SRA-VJTI/sra-board-hardware-design/documentation/assets/3d_side_view.png

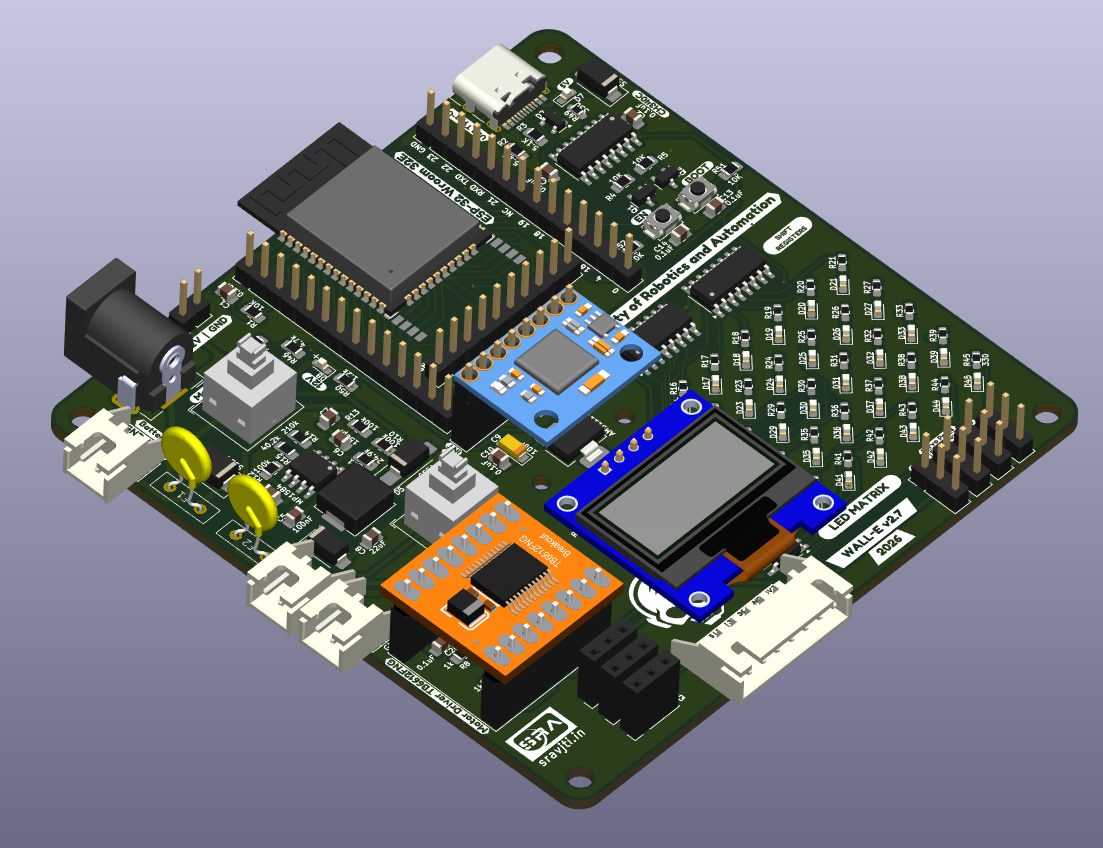
documentation/assets/3d_side_view.png
