SRA-VJTI/sra-board-hardware-design/documentation/assets/A4988_Stepper_Motor.png

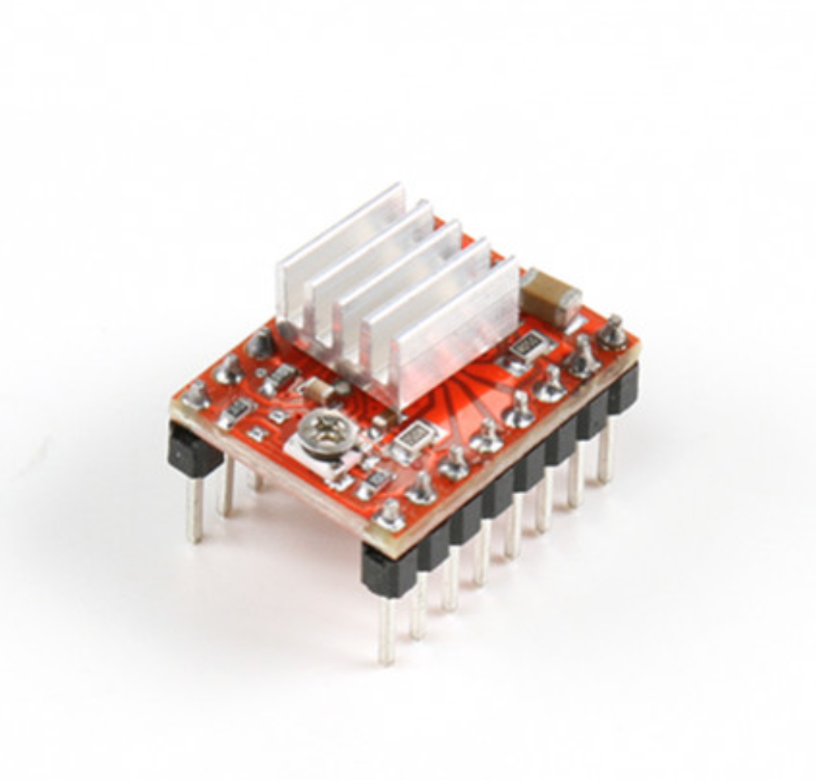
documentation/assets/A4988_Stepper_Motor.png
