SRA-VJTI/sra-board-hardware-design/documentation/assets/diode_vin.png

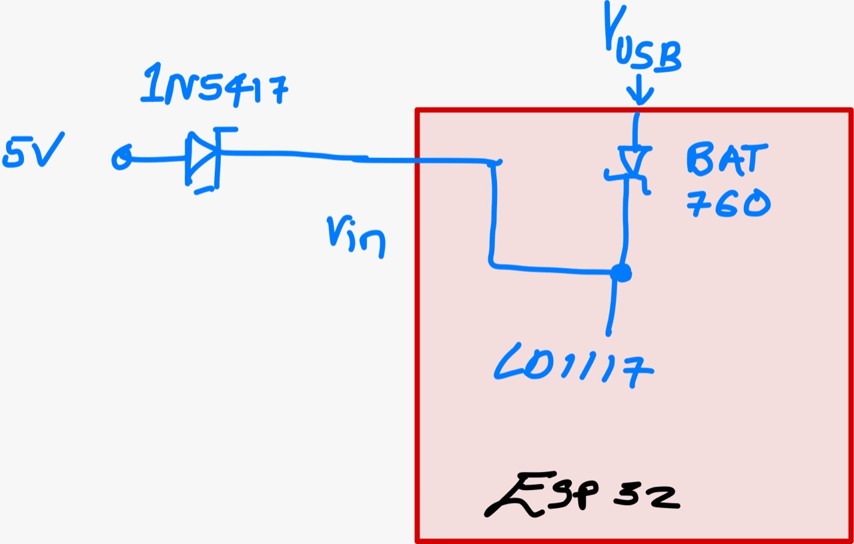
documentation/assets/diode_vin.png
