SRA-VJTI/sra-board-hardware-design/documentation/assets/normal_mode.jpeg

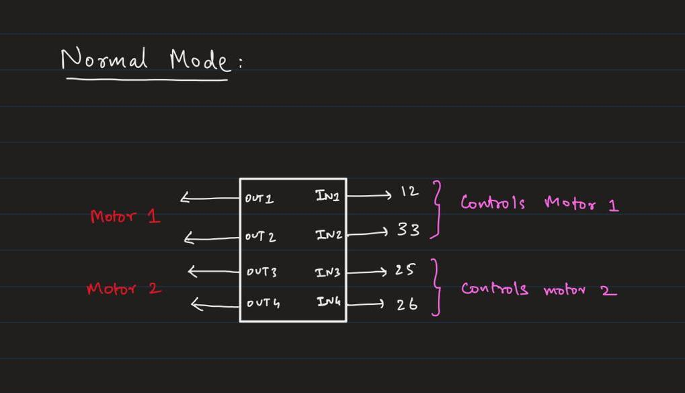
documentation/assets/normal_mode.jpeg
