SRA-VJTI/sra-board-hardware-design/documentation/assets/parallel_mode.jpeg

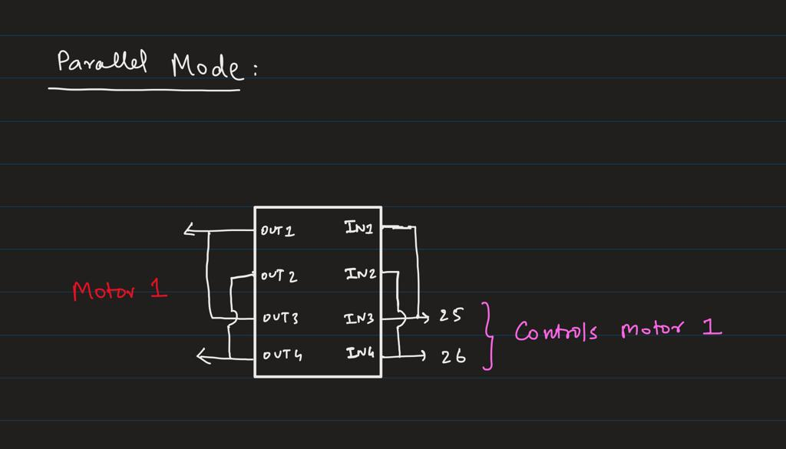
documentation/assets/parallel_mode.jpeg
