SRA-VJTI/sra-board-hardware-design/documentation/assets/sra_board_2019.png

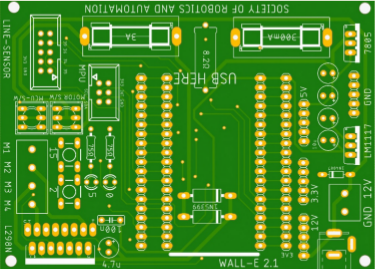
documentation/assets/sra_board_2019.png
