SRA-VJTI/sra-board-hardware-design/documentation/assets/sra_board_2021.png

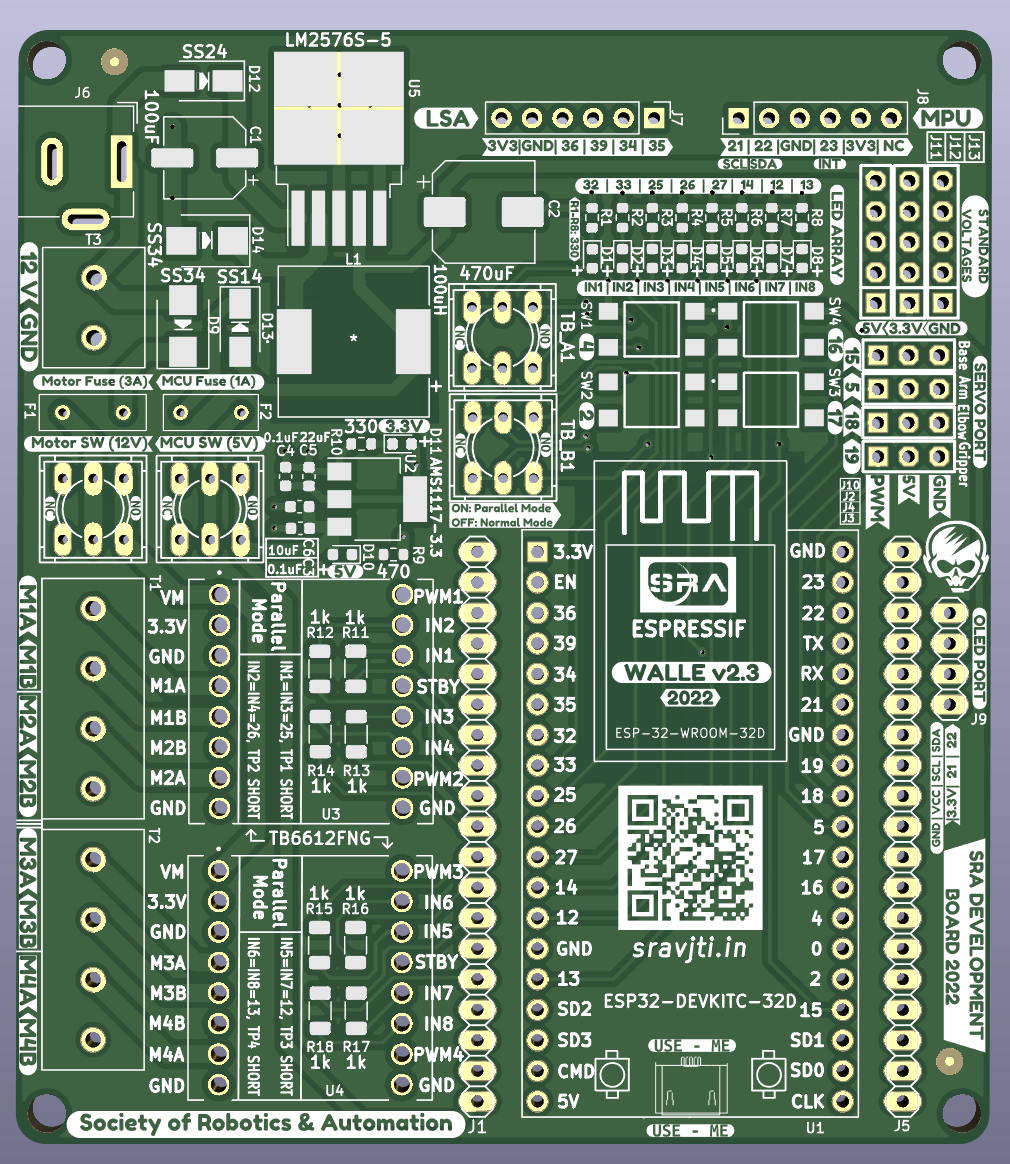
documentation/assets/sra_board_2021.png
