SRA-VJTI/sra-board-hardware-design/documentation/images/board_images/bcu.png

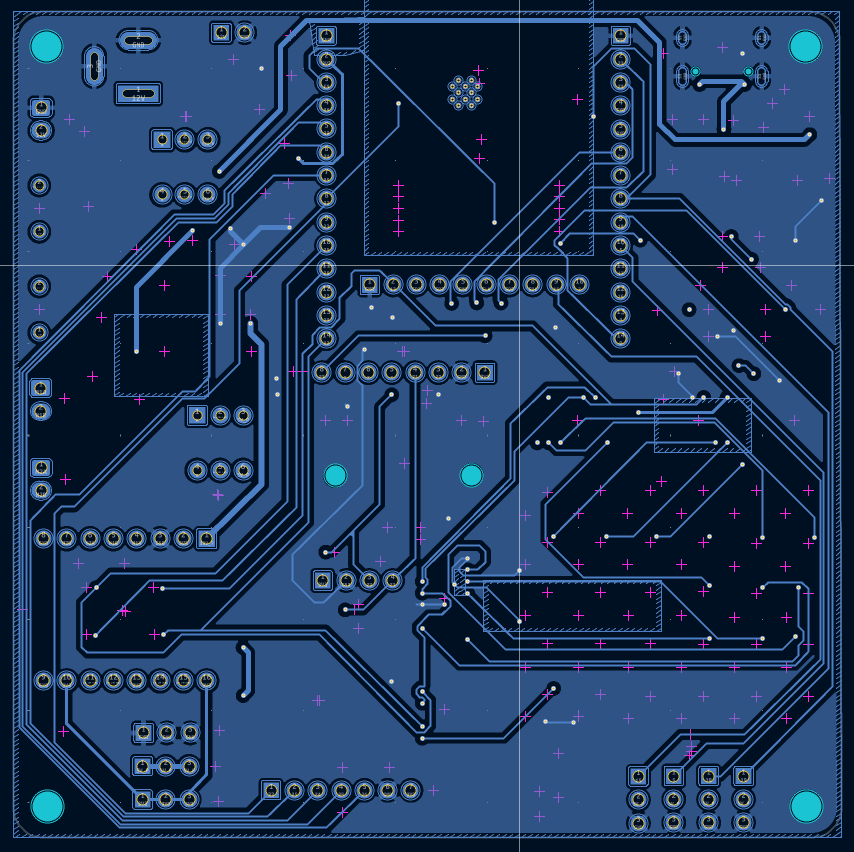
documentation/images/board_images/bcu.png
