SRA-VJTI/sra-board-hardware-design/documentation/images/board_images/front_silk_layer.png

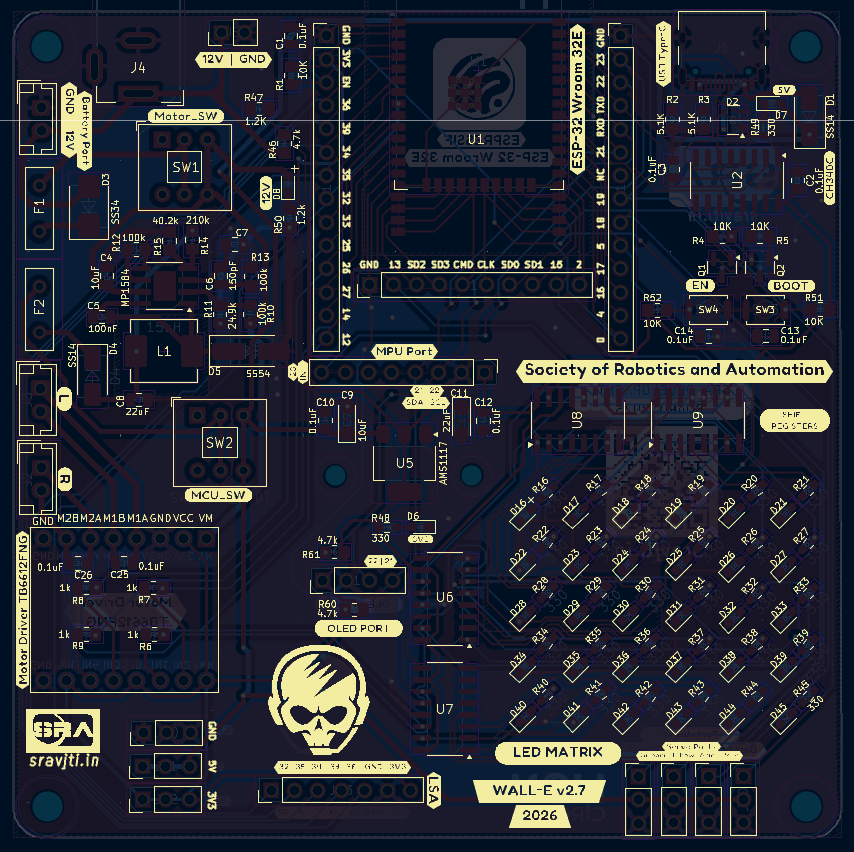
documentation/images/board_images/front_silk_layer.png
