SRA-VJTI/sra-board-hardware-design/documentation/images/LSA_images/lsa.png

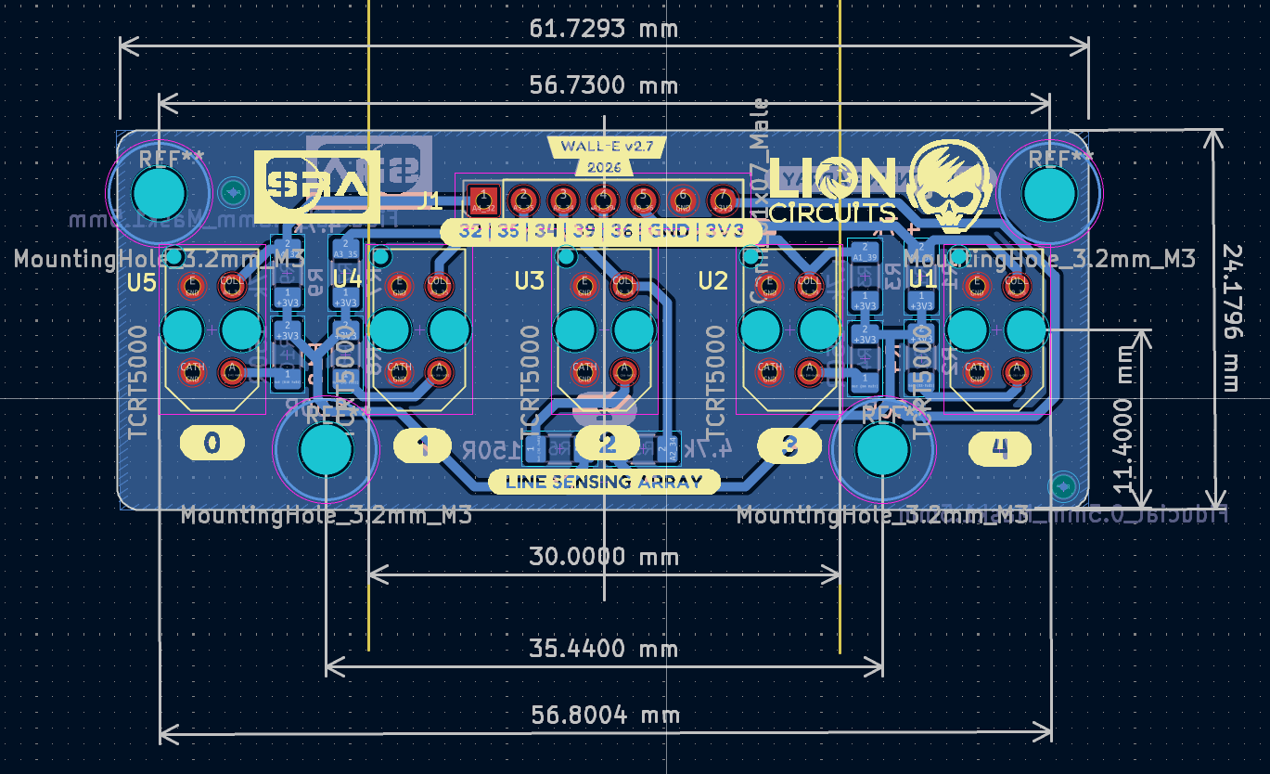
documentation/images/LSA_images/lsa.png
