SRA-VJTI/sra-board-hardware-design/documentation/images/LSA_images/Lsa_side.png

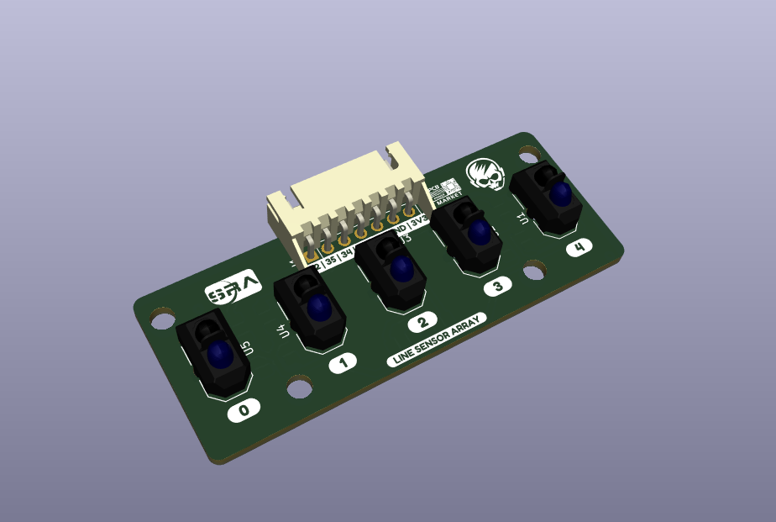
documentation/images/LSA_images/Lsa_side.png
