SRA-VJTI/sra-board-hardware-design/documentation/images/LSA_images/lsa_with_dim.png

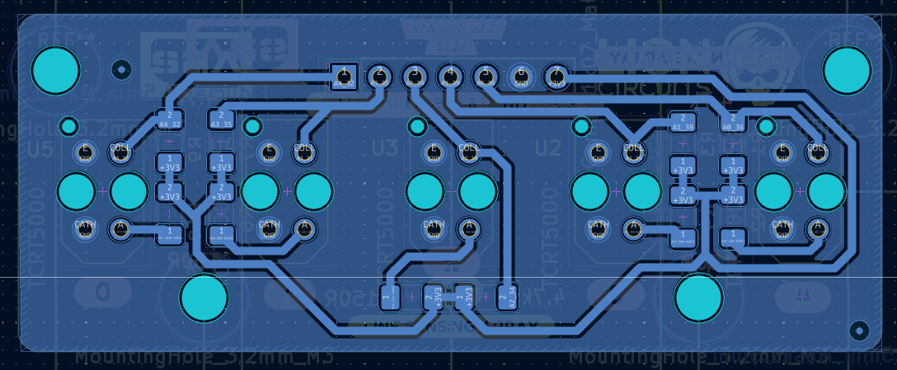
documentation/images/LSA_images/lsa_with_dim.png
