SRA-VJTI/sra-board-hardware-design/documentation/images/MPU_images/Mpu.png

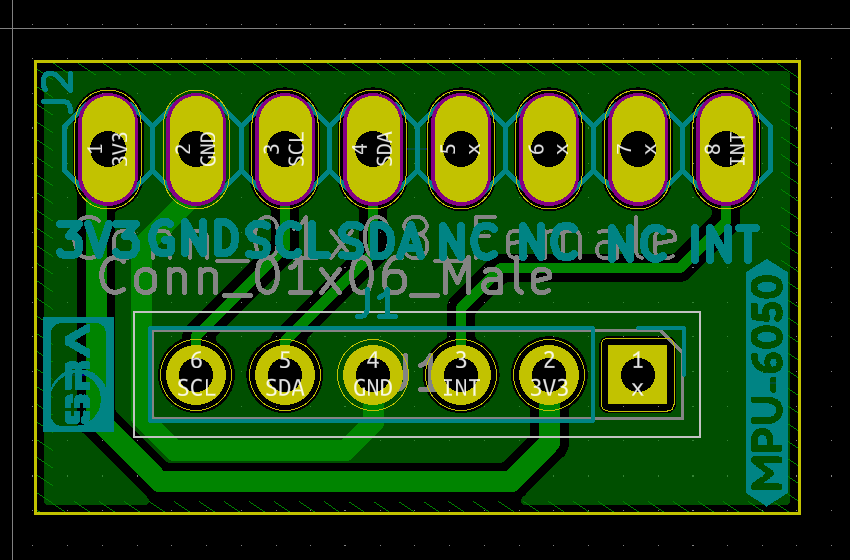
documentation/images/MPU_images/Mpu.png
