SRA-VJTI/sra-board-hardware-design/documentation/images/MPU_images/Mpu_back.png

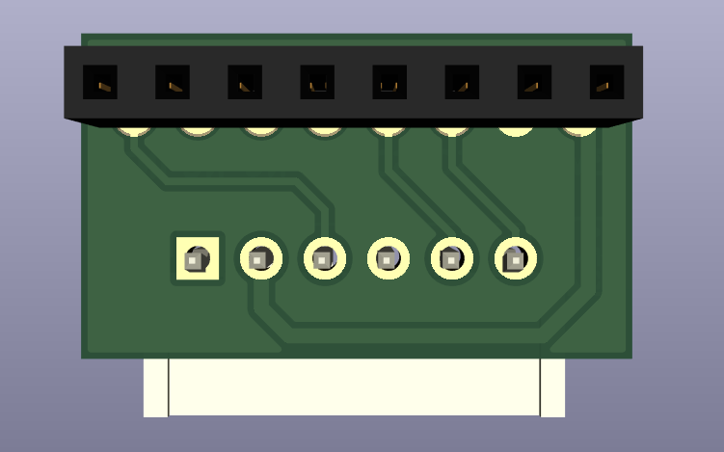
documentation/images/MPU_images/Mpu_back.png
