SRA-VJTI/sra-board-hardware-design/documentation/images/MPU_images/Mpu_front.png

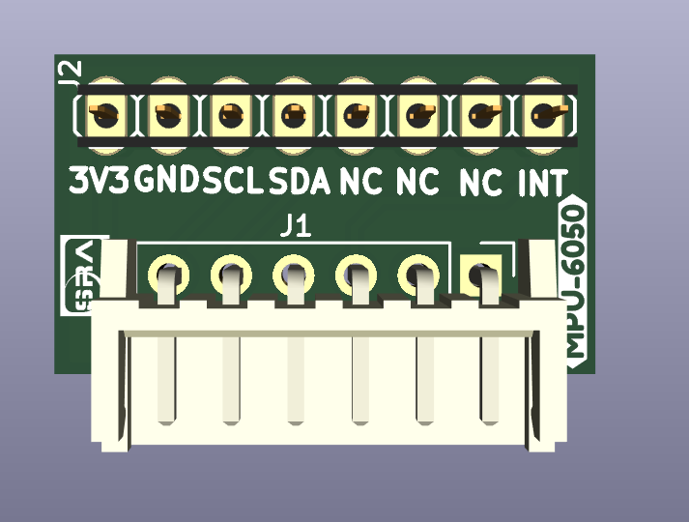
documentation/images/MPU_images/Mpu_front.png
