SRA-VJTI/sra-board-hardware-design/documentation/images/MPU_images/Mpu_side.png

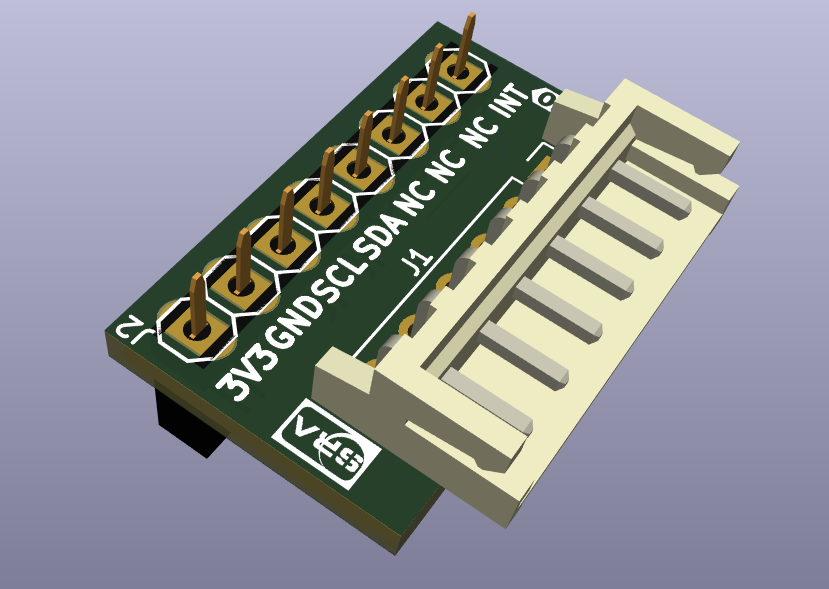
documentation/images/MPU_images/Mpu_side.png
