SRA-VJTI/sra-board-hardware-design/documentation/images/MPU_images/Mpu_with_dim.png

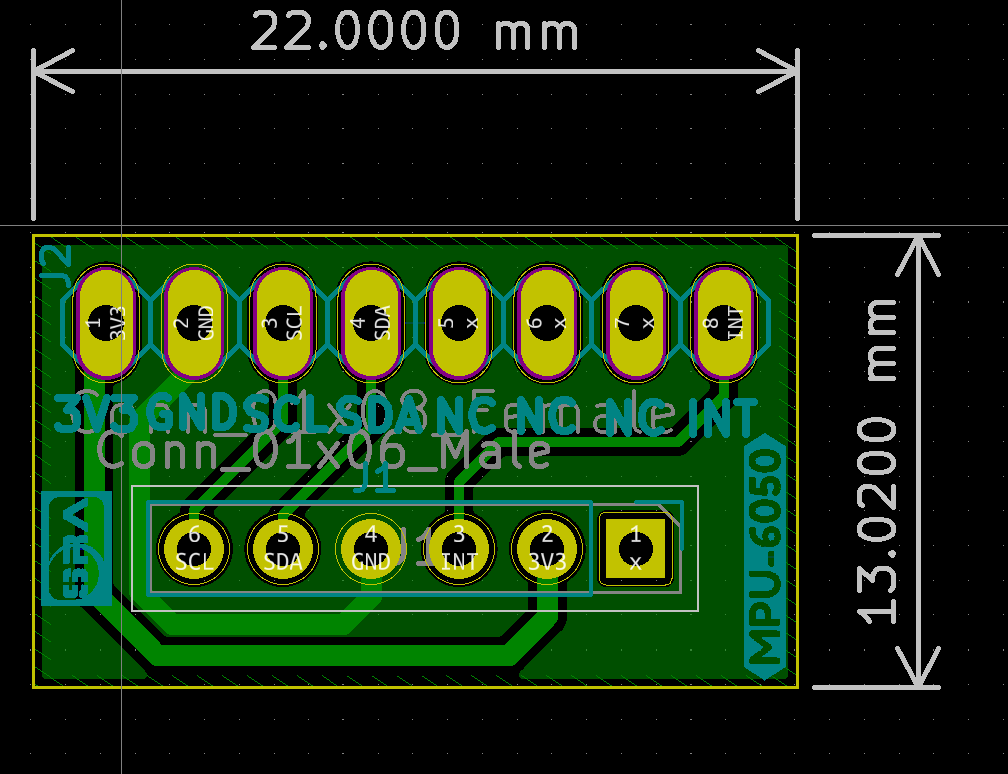
documentation/images/MPU_images/Mpu_with_dim.png
