SRA-VJTI/sra-board-hardware-design/sra_dev_board_2024/component_libraries/oled/ER-OLEDM013-1-I2C-SPI_Bottom_View.jpg

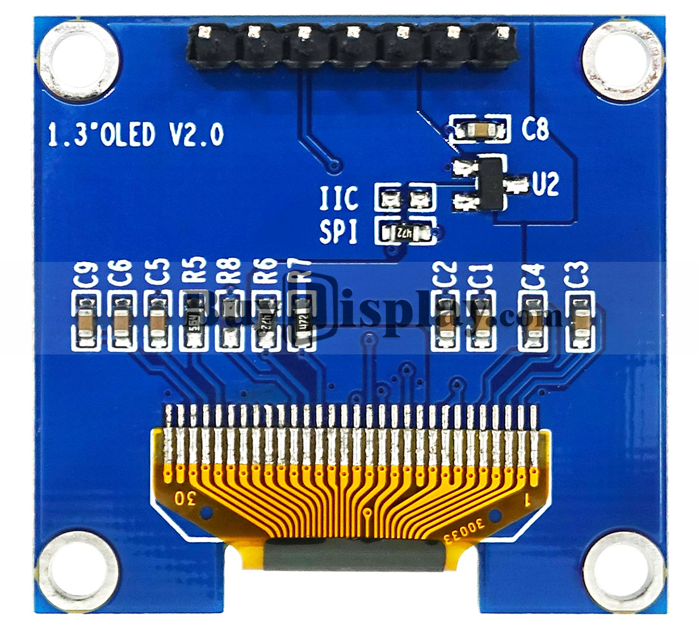
sra_dev_board_2024/component_libraries/oled/ER-OLEDM013-1-I2C-SPI_Bottom_View.jpg
