SRA-VJTI/sra-board-hardware-design/sra_dev_board_2023/component_libraries/stepper_motor_driver/A4988_STEPPER_MOTOR_DRIVER_CARRIER.step

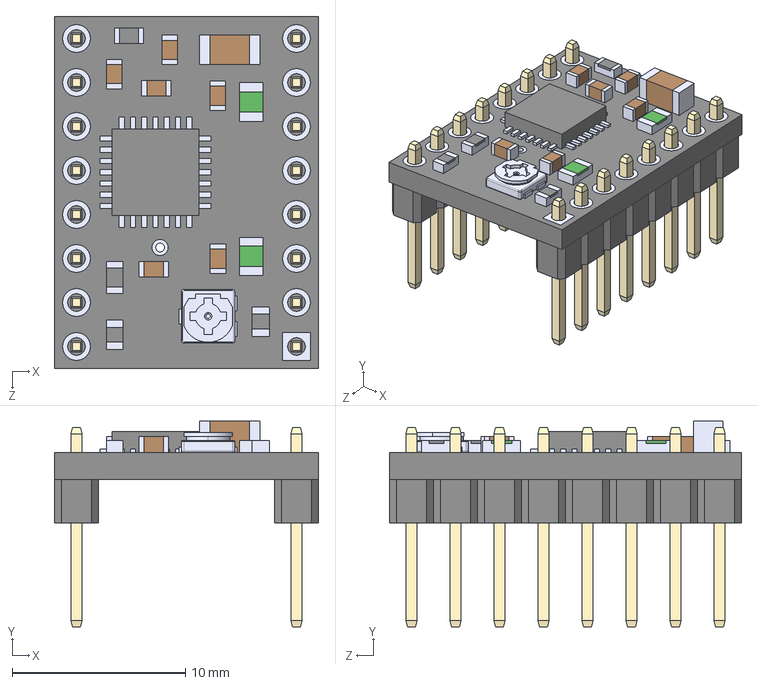
[picture p63: CAD file, 2023-01-12]
sra_dev_board_2023/component_libraries/stepper_motor_driver/A4988_STEPPER_MOTOR_DRIVER_CARRIER.step
15.2 x 11.9 x 20.3 mm
