SRA-VJTI/sra-board-hardware-design/sra_dev_board_2024/component_libraries/4407/AP4407GM.stp

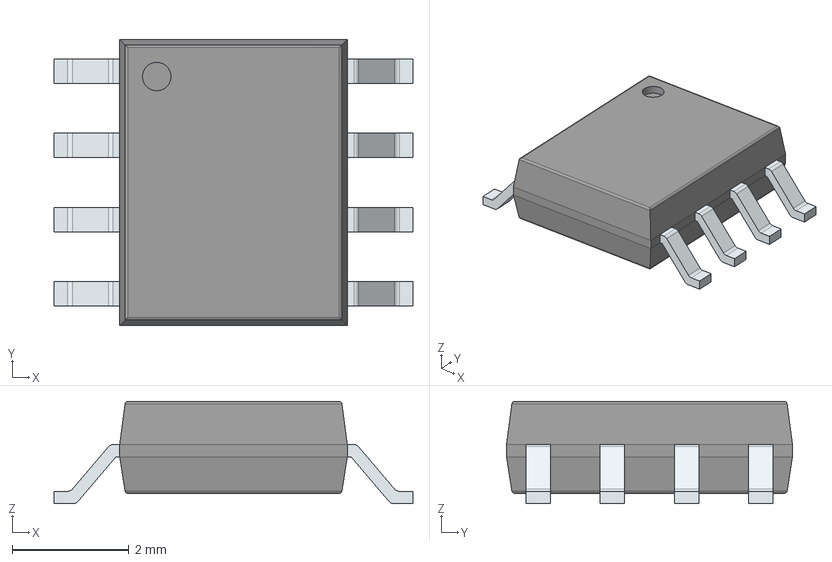
[picture p64: CAD file, 2025-04-10]
sra_dev_board_2024/component_libraries/4407/AP4407GM.stp
6.15 x 4.90 x 1.75 mm
PinsArrayLR
