SRA-VJTI/sra-board-hardware-design/sra_dev_board_2024/component_libraries/8254a/S-8254AAJFT-TB-G.stp

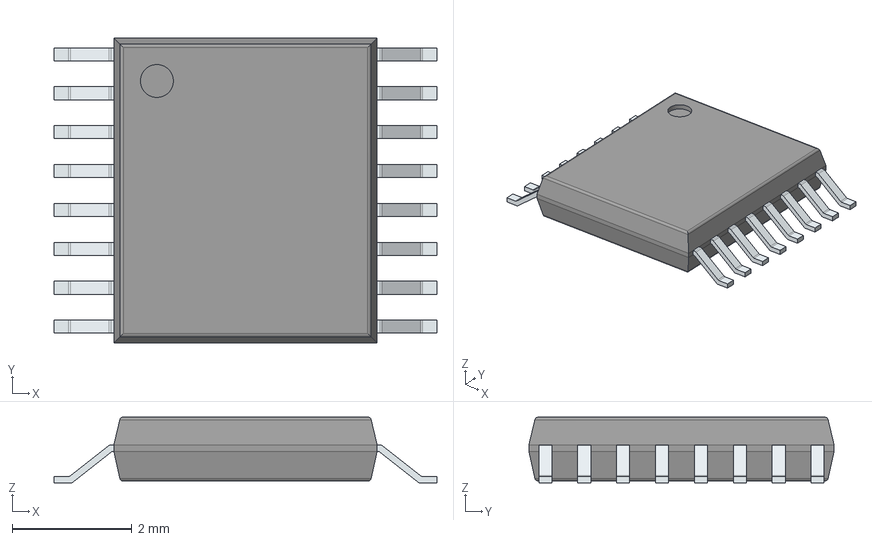
[picture p65: CAD file, 2025-04-10]
sra_dev_board_2024/component_libraries/8254a/S-8254AAJFT-TB-G.stp
6.40 x 5.10 x 1.10 mm
PinsArrayLR
