SRA-VJTI/sra-board-hardware-design/sra_dev_board_2024/component_libraries/inductor/CDRH104R_inductor_smd.stp

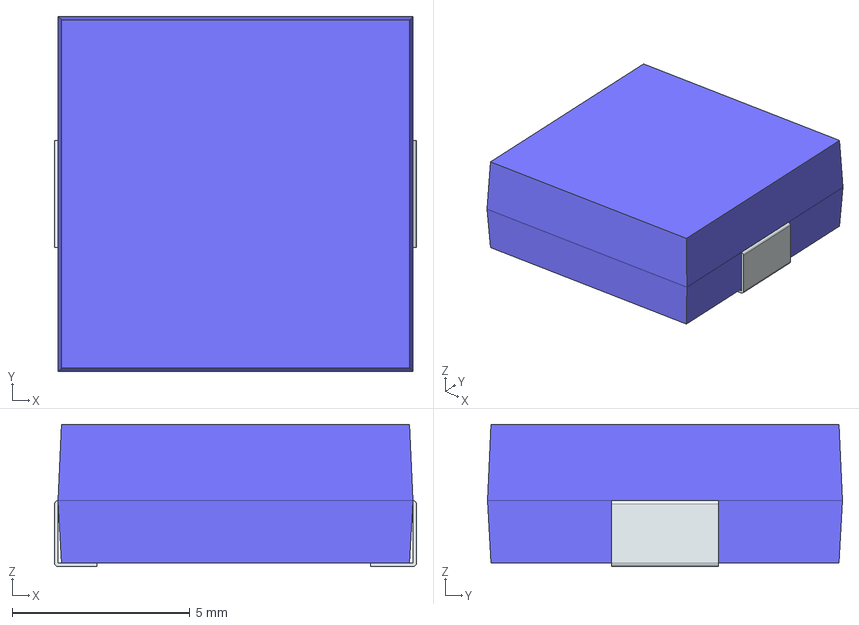
[picture p66: CAD file, 2022-01-30]
sra_dev_board_2024/component_libraries/inductor/CDRH104R_inductor_smd.stp
10.2 x 10.0 x 4.00 mm
FilletPin1
FilletPin2
