SRA-VJTI/sra-board-hardware-design/sra_dev_board_2024/component_libraries/oled/PCB v8.step

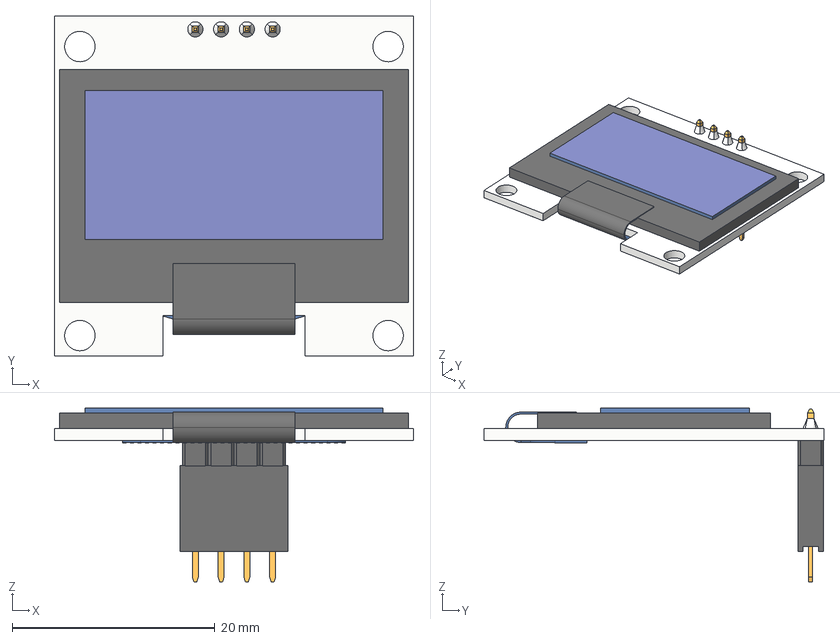
[picture p67: CAD file, 2025-04-10]
sra_dev_board_2024/component_libraries/oled/PCB v8.step
35.4 x 33.5 x 17.1 mm
Board
PIN HEADER MALE 2.54MM P4
LCD
FLEX FILM
4 lü Lehim
PIN HEADER FAMALE 2.54MM P4
