SRA-VJTI/sra-board-hardware-design/sra_dev_board_2024/component_libraries/Power JST Connector/B2B-XH-A_LF__SN_.step

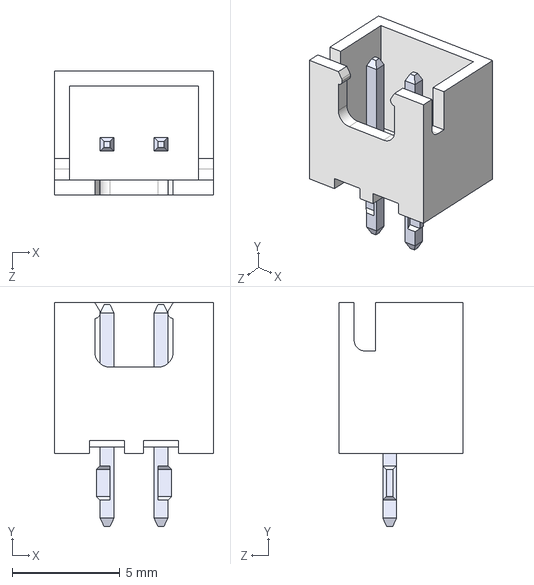
[picture p68: CAD file, 2025-04-10]
sra_dev_board_2024/component_libraries/Power JST Connector/B2B-XH-A_LF__SN_.step
7.40 x 10.4 x 5.75 mm
