SRA-VJTI/sra-board-hardware-design/sra_dev_board_2024/component_libraries/terminal_block/12V_1x02_tht.step

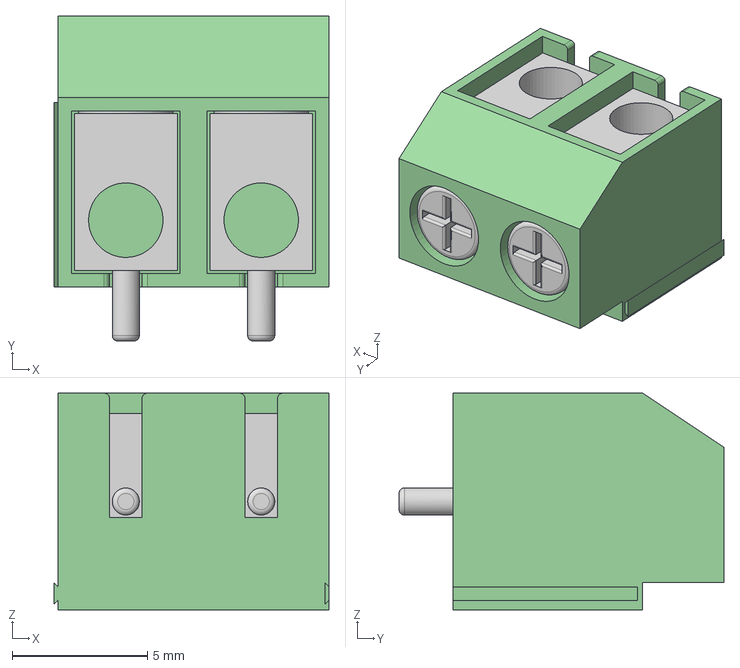
[picture p69: CAD file, 2020-09-04]
sra_dev_board_2024/component_libraries/terminal_block/12V_1x02_tht.step
10.2 x 12.0 x 8.00 mm
