SRA-VJTI/sra-board-hardware-design/sra_dev_board_2026/component_libraries/ESP32-WROOM/ESP32-WROOM-32E__4MB_HIGH_TEMP_.step

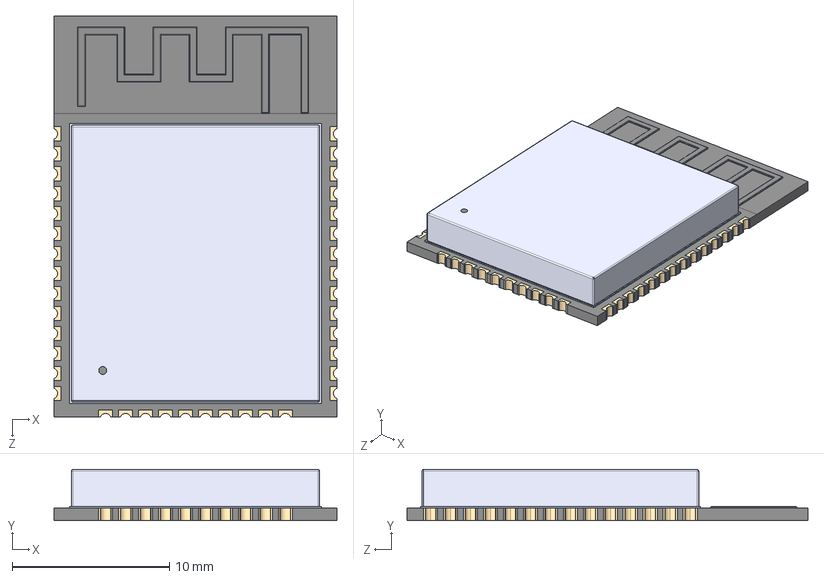
[picture p70: CAD file, 2026-03-14]
sra_dev_board_2026/component_libraries/ESP32-WROOM/ESP32-WROOM-32E__4MB_HIGH_TEMP_.step
18.0 x 3.25 x 25.5 mm
