SRA-VJTI/sra-board-hardware-design/sra_dev_board_2026/component_libraries/JST Connector/7 Pin JST_LSA/S7B-XH-A_LF__SN_.step

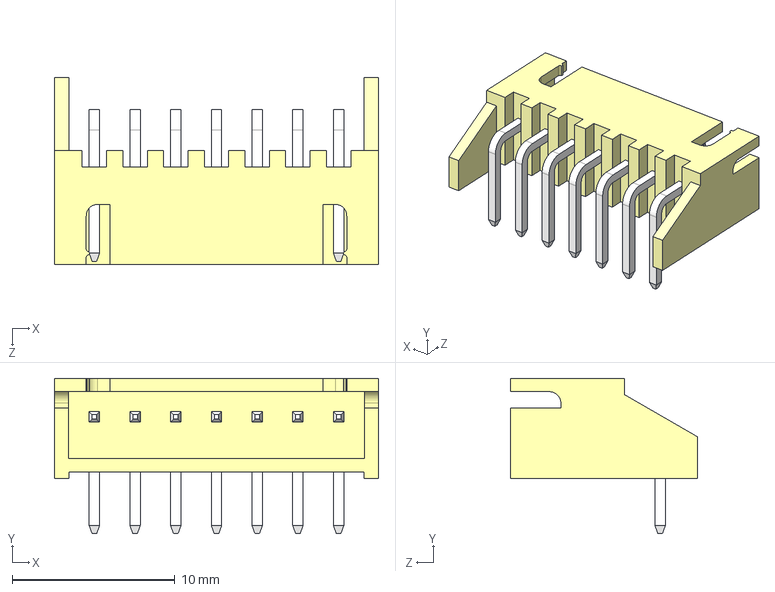
[picture p71: CAD file, 2026-03-14]
sra_dev_board_2026/component_libraries/JST Connector/7 Pin JST_LSA/S7B-XH-A_LF__SN_.step
19.9 x 9.55 x 11.5 mm
