SRA-VJTI/sra-board-hardware-design/sra_dev_board_2026/component_libraries/MCU_ESP32/ESP32-DEVKITCv4-32D.STEP

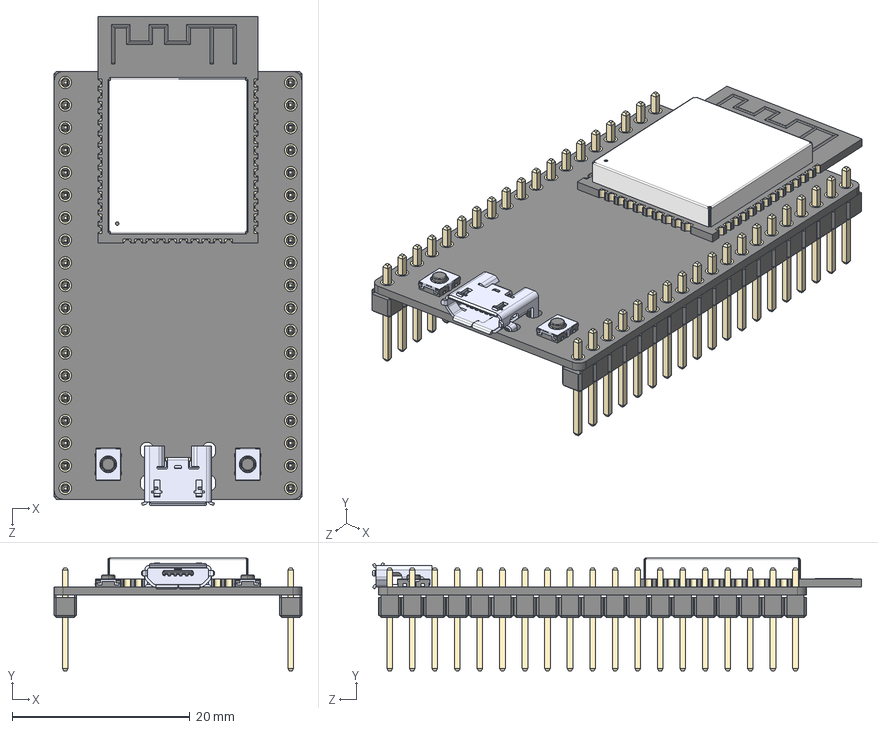
[picture p72: CAD file, 2026-03-14]
sra_dev_board_2026/component_libraries/MCU_ESP32/ESP32-DEVKITCv4-32D.STEP
27.9 x 12.7 x 55.1 mm
board
header x 2
ESP32-WROOM-32D
micro usb
button x 2
