SRA-VJTI/sra-board-hardware-design/sra_dev_board_2026/component_libraries/motor_driver/TB6612FNG.step

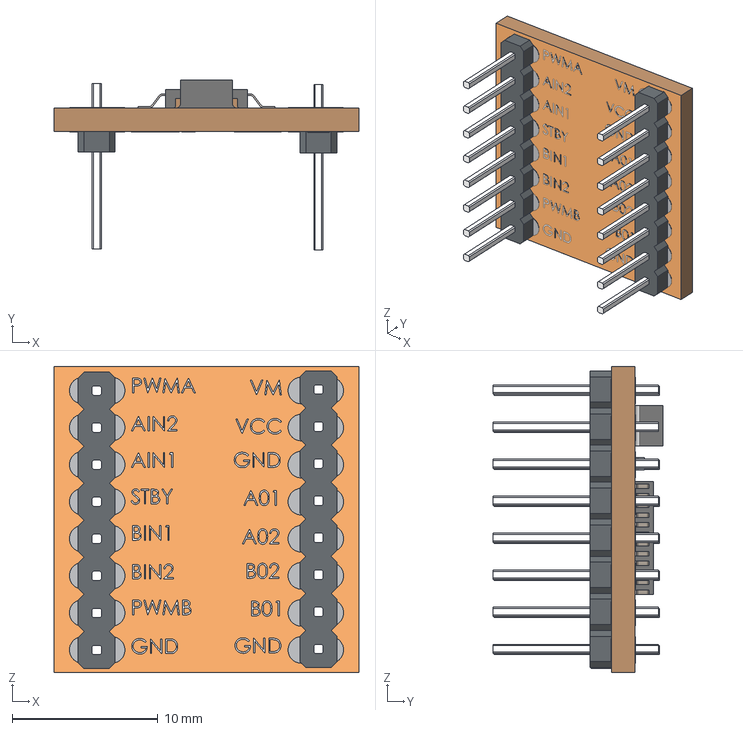
[picture p73: CAD file, 2026-03-14]
sra_dev_board_2026/component_libraries/motor_driver/TB6612FNG.step
20.9 x 11.6 x 21.0 mm
TB6612FNG Motor Driver
1x8 x 2
