SRA-VJTI/sra-board-hardware-design/sra_dev_board_2026/component_libraries/MPU/MPU6050/MPU6050 v2.step

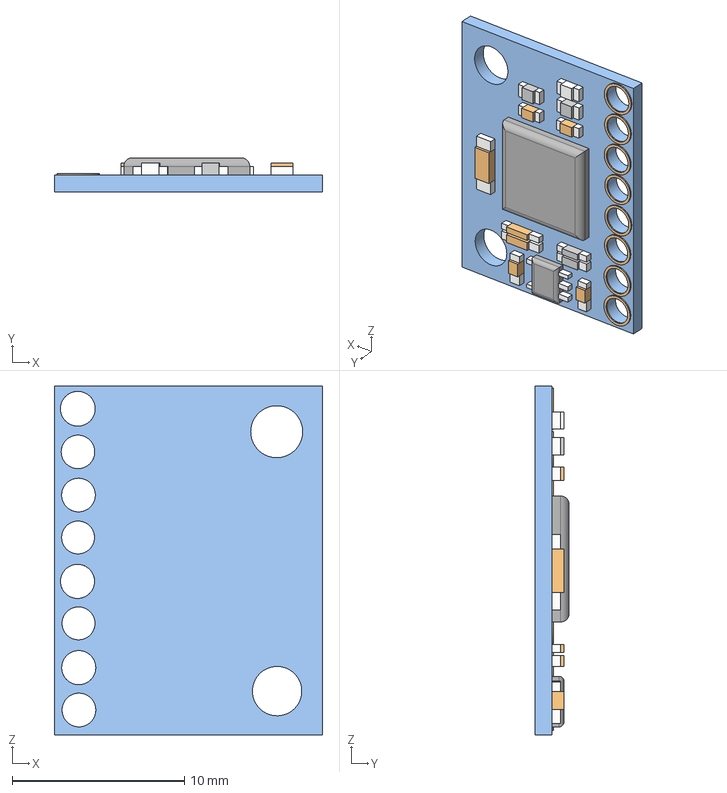
[picture p74: CAD file, 2026-03-14]
sra_dev_board_2026/component_libraries/MPU/MPU6050/MPU6050 v2.step
15.6 x 2.00 x 20.3 mm
