SRA-VJTI/sra-board-hardware-design/sra_dev_board_2026/component_libraries/ptc_fuse/RXEF050_1A_trip/RUEF.step

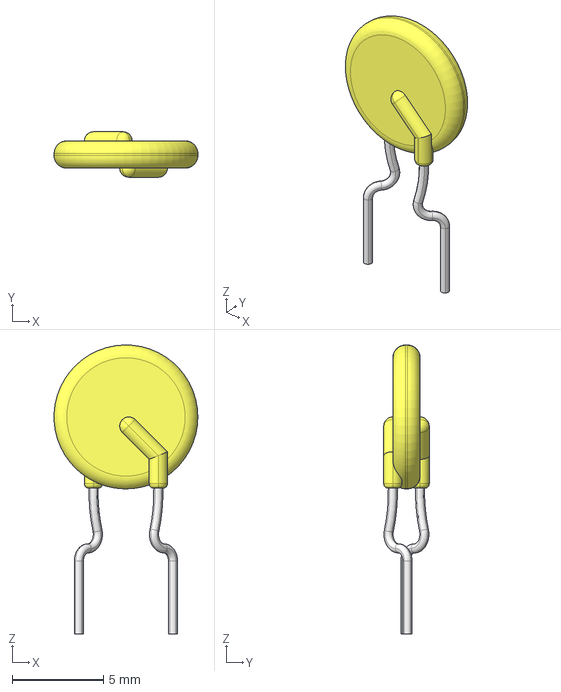
[picture p75: CAD file, 2026-03-14]
sra_dev_board_2026/component_libraries/ptc_fuse/RXEF050_1A_trip/RUEF.step
7.89 x 2.50 x 15.9 mm
