SRA-VJTI/sra-board-hardware-design/sra_dev_board_2026/component_libraries/switches/Esp-32 Switch/skrkaee010.stp

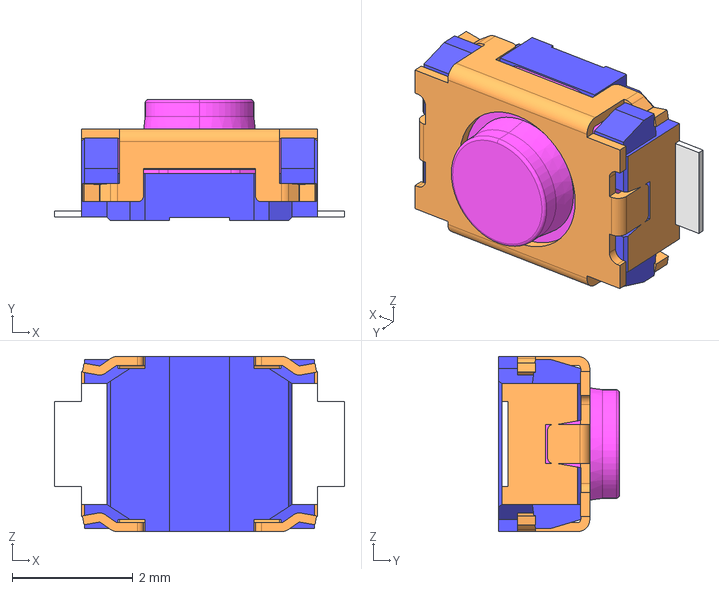
[picture p76: CAD file, 2026-03-14]
sra_dev_board_2026/component_libraries/switches/Esp-32 Switch/skrkaee010.stp
4.80 x 2.00 x 2.90 mm
