SRA-VJTI/sra-board-hardware-design/3d_models/lsa_model/lsa-2024.step

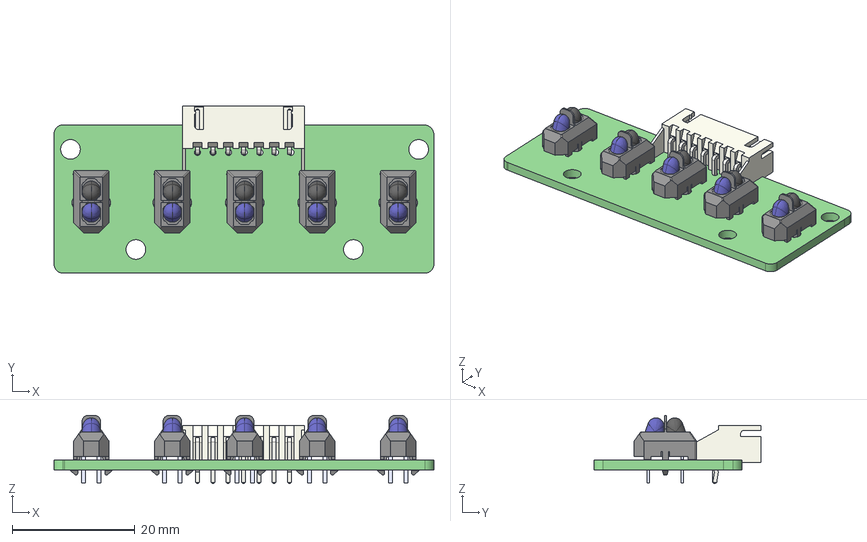
[picture p77: CAD file, 2023-01-12]
3d_models/lsa_model/lsa-2024.step
61.9 x 27.3 x 11.1 mm
lsa PCB
