SRA-VJTI/sra-board-hardware-design/sra_dev_board_2026/component_libraries/MCU_ESP32/ESP32-WROVER.step

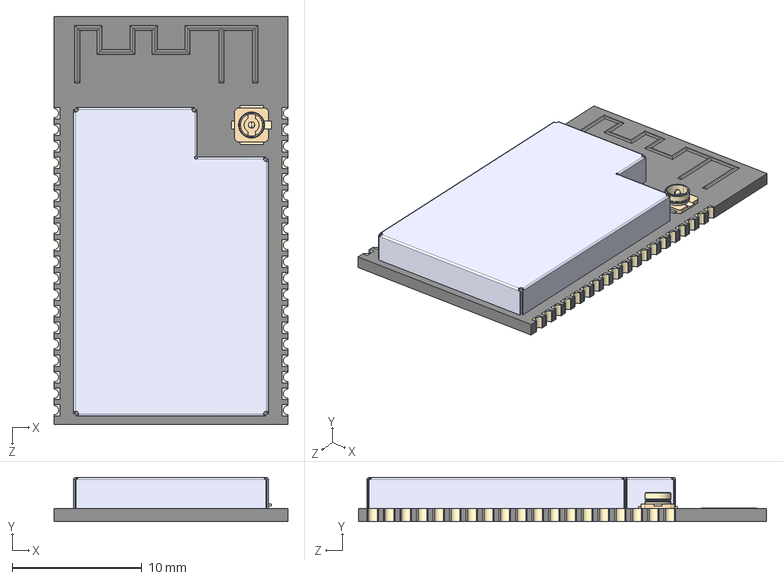
[picture p78: CAD file, 2026-03-14]
sra_dev_board_2026/component_libraries/MCU_ESP32/ESP32-WROVER.step
18.0 x 3.40 x 31.4 mm
